ValerianGregoire/microwave_pcb/PCB/v1/Schematic.pdf

# Microwave Control Panel

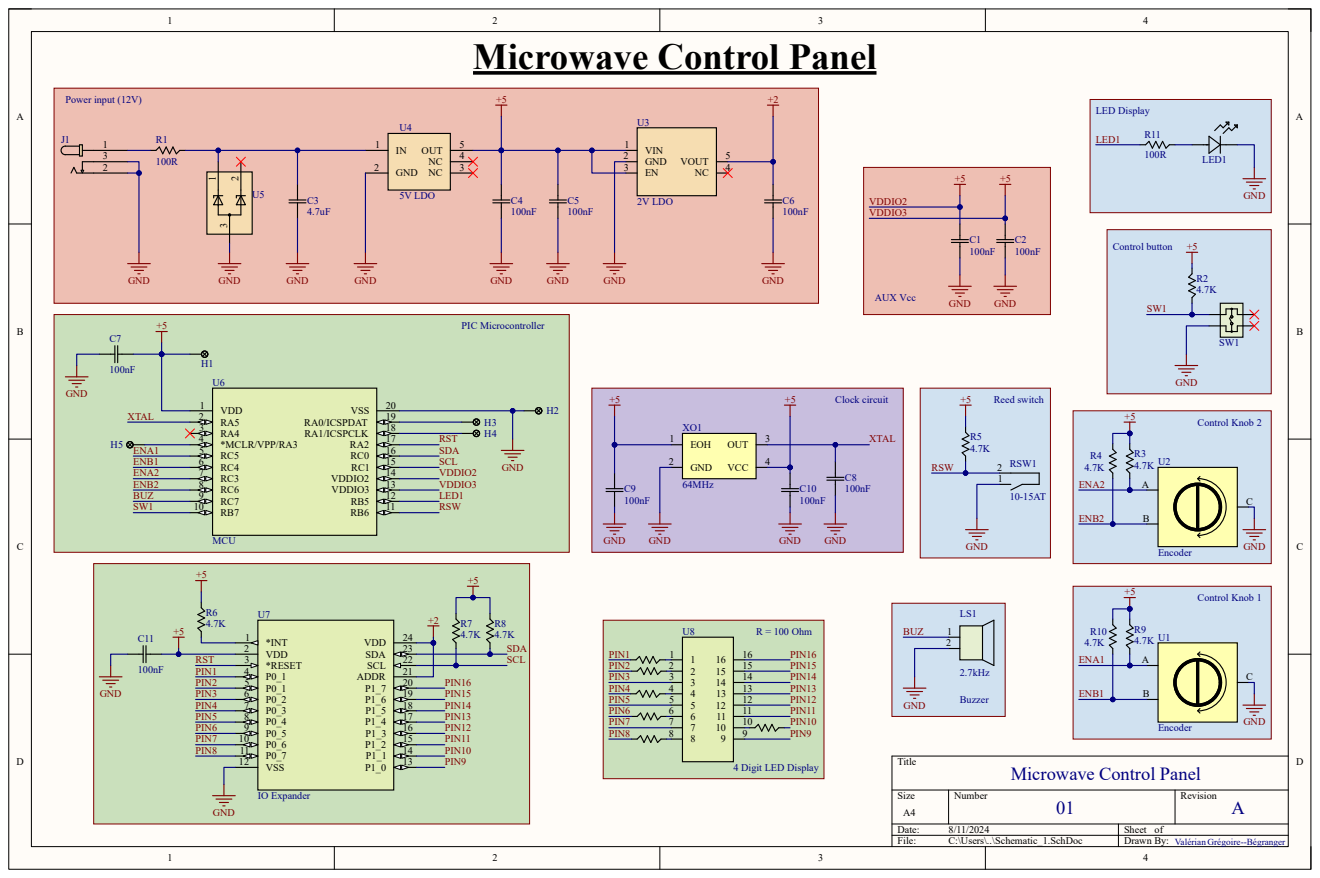
[picture p46: page 1]
