ValerianGregoire/microwave_pcb/Software/src/base.h

#ifndef __BASE
#define __BASE

#include <stdint.h>
#include <stdlib.h>
#include <math.h>
#include <stdio.h>

#define ERROR 0
#define SUCCESS 1
#define RETRY 2
#define ABORT 3

#define DEBUG_STATE


#endif
